Reikimen/CASA0021-Group-Prototype/Img/Groupmeeting/week2/WhatsApp Image 2025-02-03 at 17.10.47.jpeg

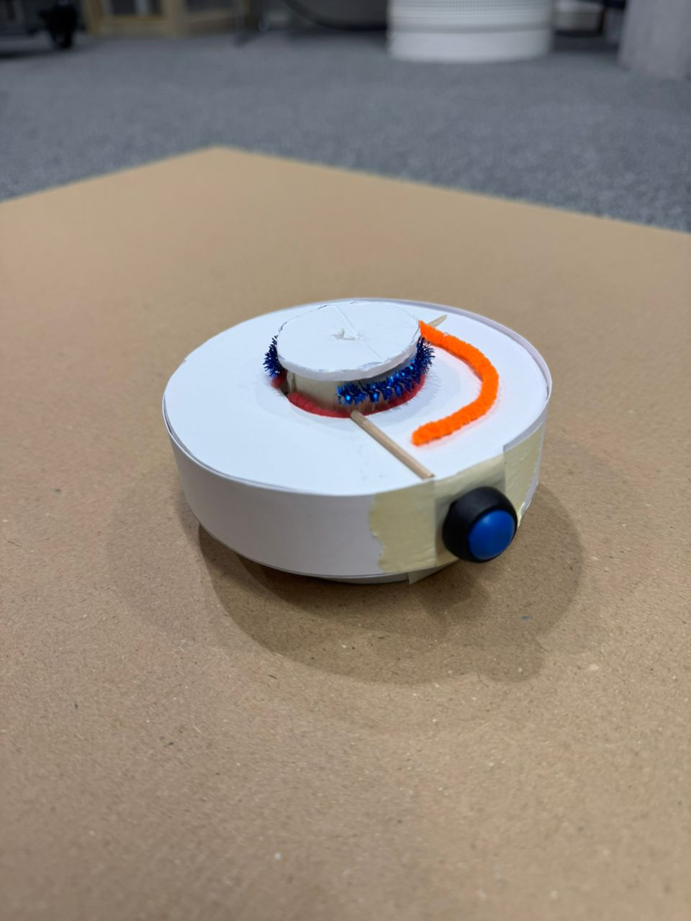
Img/Groupmeeting/week2/WhatsApp Image 2025-02-03 at 17.10.47.jpeg
