Reikimen/CASA0021-Group-Prototype/Img/Groupmeeting/week2/WhatsApp Image 2025-02-03 at 22.30.48 (1).jpeg

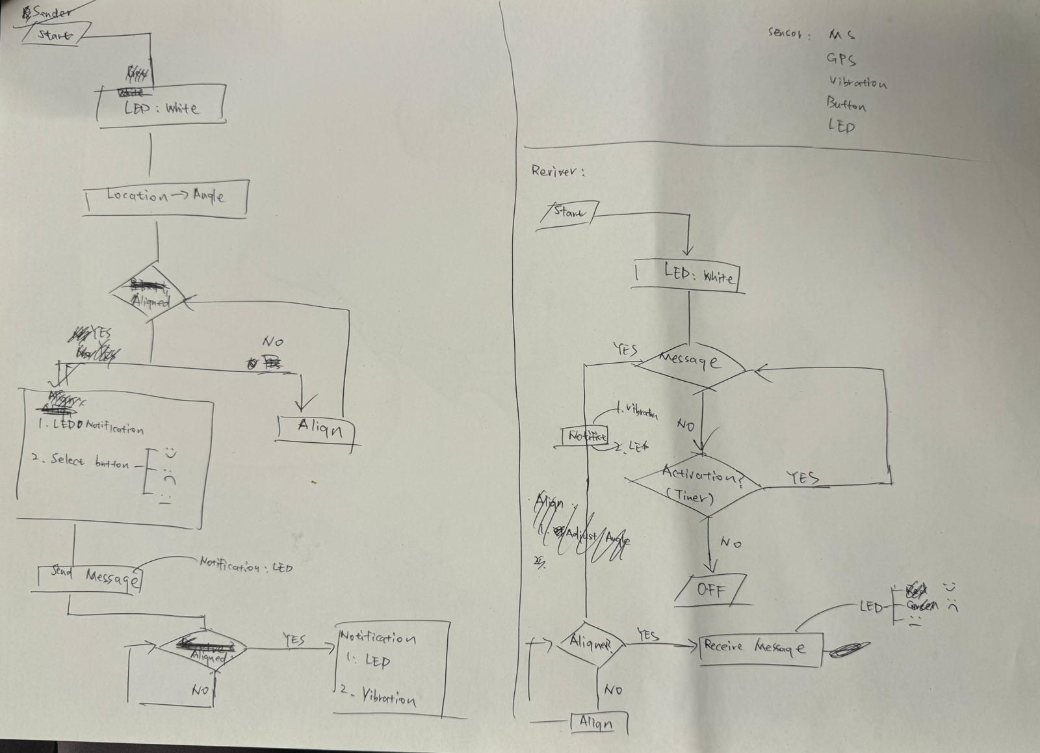
Img/Groupmeeting/week2/WhatsApp Image 2025-02-03 at 22.30.48 (1).jpeg
